mrcory/Roller-Shade-Controller/shade_controller/functions.h

bool isOpened = true;

void configSave() {
  //Position 400 is reserved for the blynk token
  EEPROM.write(0,1); //Flag for autoload
  EEPROM.put(3,configVersion);
  int i=5;
  EEPROM.put(i,savedPosition);
  i+=sizeof(savedPosition);
  EEPROM.put(i,lastPosition);
  i+=sizeof(lastPosition);
  EEPROM.put(i,mInvert.was);
  i+=sizeof(mInvert.was);
  EEPROM.put(i,pwm.set);
  i+=sizeof(pwm.set);
  EEPROM.put(i,mInvert.set);
  i+=sizeof(mInvert.set);
  EEPROM.put(i,mSpeed.up);
  i+=sizeof(mSpeed.up);
  EEPROM.put(i,mSpeed.dn);
  i+=sizeof(mSpeed.dn);
  EEPROM.put(i,mSpeed.accel);
  i+=sizeof(mSpeed.accel);
  EEPROM.put(i,ledButtonBrightness);
  i+=sizeof(ledButtonBrightness);
  EEPROM.commit();
  Serial.println("Config Saved");
}

void configLoad() {
  int i=5;
  EEPROM.get(5,savedPosition);
  i+=sizeof(savedPosition);
  EEPROM.get(i,lastPosition);
  i+=sizeof(lastPosition);
  EEPROM.get(i,mInvert.was);
  i+=sizeof(mInvert.was);
  EEPROM.get(i,pwm.set);
  i+=sizeof(pwm.set);
  EEPROM.get(i,mInvert.set);
  i+=sizeof(mInvert.set);
  EEPROM.get(i,mSpeed.up);
  i+=sizeof(mSpeed.up);
  EEPROM.get(i,mSpeed.dn);
  i+=sizeof(mSpeed.dn);
  EEPROM.get(i,mSpeed.accel);
  i+=sizeof(mSpeed.accel);
  EEPROM.get(i,ledButtonBrightness);
  i+=sizeof(ledButtonBrightness);
  Serial.println("Config Loaded");
  Serial.println(savedPosition);
}

void ledFeedbackf() {

  if (ledMode == 0) {
    if (ledTimer > millis() - 500) {
      digitalWrite(ledPin, HIGH);
    } else {
      digitalWrite(ledPin, LOW);
    }   
  } 

  if (ledMode == 1) {
    if (ledTimer > millis() - 1500) {
      digitalWrite(ledPin, HIGH);
    } else {
      digitalWrite(ledPin, LOW);
    }
  }

  if (ledMode == 2) {
    if (ledTimer > millis() - 1000) {
      if ((millis() > ledTimer + 250) && (millis()  < ledTimer + 750)) {
        digitalWrite(ledPin, LOW);
      } else {
        digitalWrite(ledPin, HIGH);
      }
  } else {
        digitalWrite(ledPin, LOW);
   }
}
}

void ledTurn(int _mode) {
    ledTimer  = millis();
    ledFeedback = true;
    ledMode = _mode;
}

#ifdef Blynkenable
  //We will conigure Blynk with this
  void blynkConfig (){
    Blynk.config(auth,server,port);
  
    #if !(defined(wifiManagerEnabled))
      Blynk.connectWiFi(ssid,pass);
    #endif
  }
  
  //This will connect or run blynk
  void blynkRun() {
    if (Blynk.connected() == true) {
      Blynk.run();
      if (connectTimeout != 0) {
        connectAttempt = 0; //Reset timeout counter if successfully connected
      }
    } else {
      if (connectAttempt < connectTimeout) {
        Serial.print(F("[BLYNK] Attempting to connect... | Attempt #")); Serial.println(connectAttempt);
        Blynk.connect(3000); //Attempt to connect for 3 seconds.
        if (Blynk.connected() == true) {Serial.println(F("[BLYNK] Connected!"));}
        connectAttempt++; //Increment timeout timer
      }
    }
  
    #if rtcBlynk
     timer1.run(); //Blynk RTC
   #endif
   
    sendBlynk();
    stepPosition = posNow + stepper.distanceToGo();
  }
#endif


void speedCheck() { //Set speed based on direction

if (motorPos != 5) {
  if (goDown == true) {
    stepper.setMaxSpeed(mSpeed.dn);
  } else {
    stepper.setMaxSpeed(mSpeed.up);
  }
} else {
  stepper.setMaxSpeed(mSpeed.dn);
}

  
  stepper.setAcceleration(mSpeed.accel);  //Update acceleration
}

void checkInvert() {
  if (mInvert.is != mInvert.set) {
    for (int i=1;i<=3;i++) {
      shade[i] = shade[i]*-1;
    }
    mInvert.is = mInvert.set; //Set change flag
    Serial.print("Direction ");
      if (mInvert.is == true) {
        Serial.println("Inverted"); 
      } else {
        Serial.println("Reverted");
      }
      if (mInvert.was != mInvert.set) {mInvert.was = mInvert.set; resetFlag = true;}
      configSave();
  }
}

void motorControl() {
  checkInvert(); //Check if speeds need to be reversed

  //If motor has reached it's target location, run this
  if (stepper.distanceToGo() == 0) {
    motorOff();   

    //After movement is complete, write the current position to flash
    //This will preserve the position of the motor through power loss
    if (savedPosition != stepper.currentPosition()) {
      savedPosition = stepper.currentPosition();
      configSave();
      Serial.print(F("Position S|C : ")); Serial.print(savedPosition); Serial.print("|"); Serial.println(stepper.currentPosition());
    }
  }

  //Blynk will set a vale to motorPos that is used to set where the motor should run to
  if (motorPos > 0) {
    if (lastPosition < motorPos) {goDown = true;} else {goDown = false;}
    speedCheck();
    
    if (motorPos == 1) {stepper.moveTo(shade[0]); isOpened = true;}
    if (motorPos == 2) {stepper.moveTo(shade[1]); isOpened = false;}
    if (motorPos == 3) {stepper.moveTo(shade[2]); isOpened = false;}
    if (motorPos == 4) {stepper.moveTo(shade[3]); isOpened = false;}
    if (motorPos == 5) {stepper.moveTo(shade[4]); isOpened = false;}
    Serial.println(F("Blynk Move"));
    lastPosition = motorPos; //Before reseting motorPos, save a copy to lastPosition
    motorPos = 0; //Reset motorPos
  }
   
}

//Commands for controlling over Serial Monitor
#if cmds
  //Function used to control the motor position via Serial
  void manualMove(int arg_cnt, char **args) {
    stepper.moveTo(cmdStr2Num(args[1], 10));
    Serial.print(F("Manual Move: ")); Serial.println(cmdStr2Num(args[1], 10));
  }
  
  //Set home position via Serial
  void homePos(int arg_cnt, char **args) {
    stepper.setCurrentPosition(0);
  }
  
  //Move to position via Serial
  void pos(int arg_cnt, char **args) {
    if (cmdStr2Num(args[1],10) > 0 && cmdStr2Num(args[1],10) < 5) {
      motorPos = cmdStr2Num(args[1],10);
      Serial.print("Target Position: "); Serial.println(cmdStr2Num(args[1],10));
      
    } else {
      Serial.println("Invalid Input. (1-4 are valid.)");
    }
  }
#endif

unsigned long timer = millis();

bool timerFunc(int _comp) {
  if (millis() - timer >= _comp) {
    return true;
    timer = millis();
  } else {
    return false;
  }
}

byte returnConfigVersion() {
  byte grabbedVersion;
  EEPROM.get(3,grabbedVersion);
  return grabbedVersion;
}
